Vateva/Esp32VoiceTuner/include/audioprocessing.h

#ifndef AUDIOPROCESSING_H
#define AUDIOPROCESSING_H

#include "config.h"

// audio filtering functions
void initAudioFilters();
void recalculateAudioFilters();  // recalculate filters when parameters change
void calculateButterworthCoefficients(float cutoffHz, float sampleRate, bool isHighpass, IIRFilter* filter);
float applyIIRFilter(float input, IIRFilter* filter);
void applyPrefiltering(float* samples, uint16_t sampleCount);

// audio capture and processing functions
bool initI2S();
bool captureRealAudio(AudioBuffer* buffer);
int findCoarsePeriodYIN(const AudioBuffer* input, TuningResult* result);
bool yinAnalysis(const AudioBuffer* input, TuningResult* output, int hintedPeriod);
void convertFrequencyToNote(float frequency, char* noteName, size_t nameSize);
int calculateCentsOffset(float frequency);
bool applySmoothingToResult(TuningResult* result, const AudioBuffer* buffer);

// scale-based note conversion functions
void buildScaleNotes(int scaleType, int rootNote, int* scaleNotes, int* noteCount);
int findNearestScaleNote(float frequency, int scaleType, int rootNote);
void convertFrequencyToScaleNote(float frequency, char* noteName, size_t nameSize, int scaleType, int rootNote, int noteNaming);
int calculateScaleCentsOffset(float frequency, int scaleType, int rootNote);

#endif // AUDIOPROCESSING_H
